belarbiabdelouahab88-afk/ATCE_BATTLE/INPUT capture/Graphe/1pps.PNG

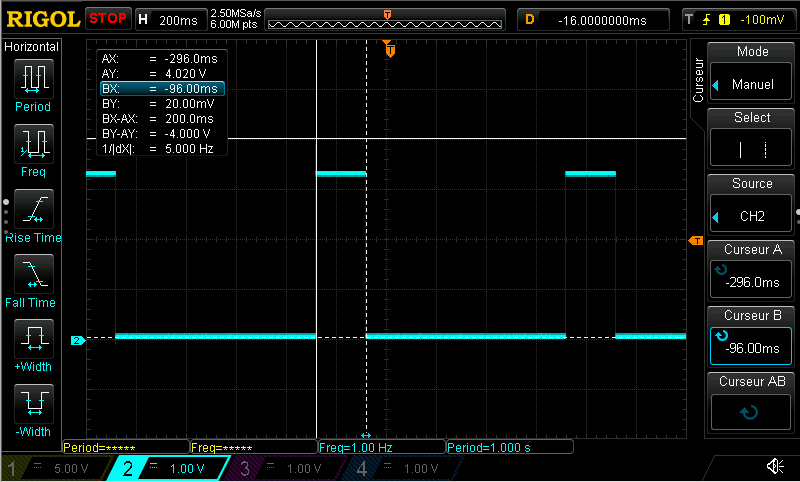
INPUT capture/Graphe/1pps.PNG
